OccasionalThingMaker/rudder-pedals/Pictures/3.jpg

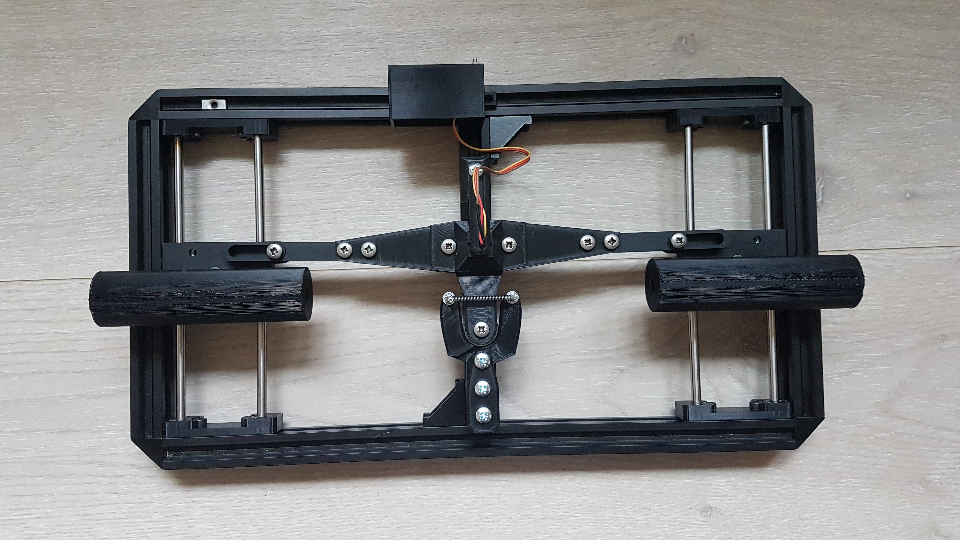
Pictures/3.jpg
