OccasionalThingMaker/rudder-pedals/STLs/Arm Extender to Carriage Bearing.stl

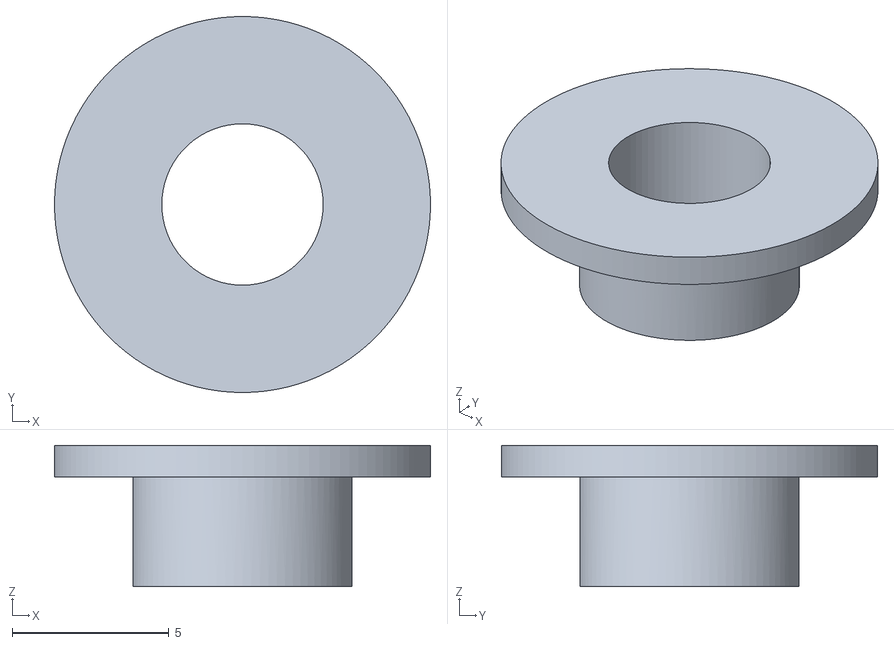
[picture p27: CAD file, 2020-10-21]
STLs/Arm Extender to Carriage Bearing.stl
12.0 x 12.0 x 4.50
