OccasionalThingMaker/rudder-pedals/STLs/Bodnar Box.stl

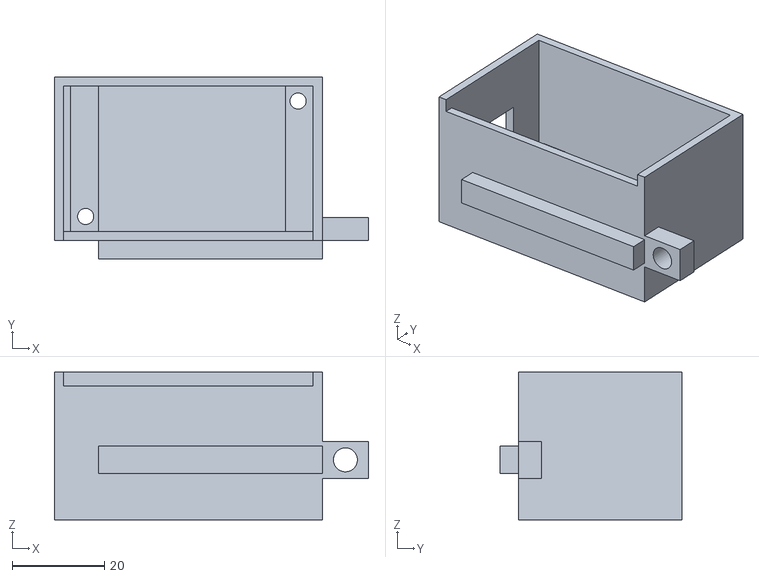
[picture p28: CAD file, 2020-10-21]
STLs/Bodnar Box.stl
68.0 x 39.5 x 32.0
