OccasionalThingMaker/rudder-pedals/STLs/seesaw.stl

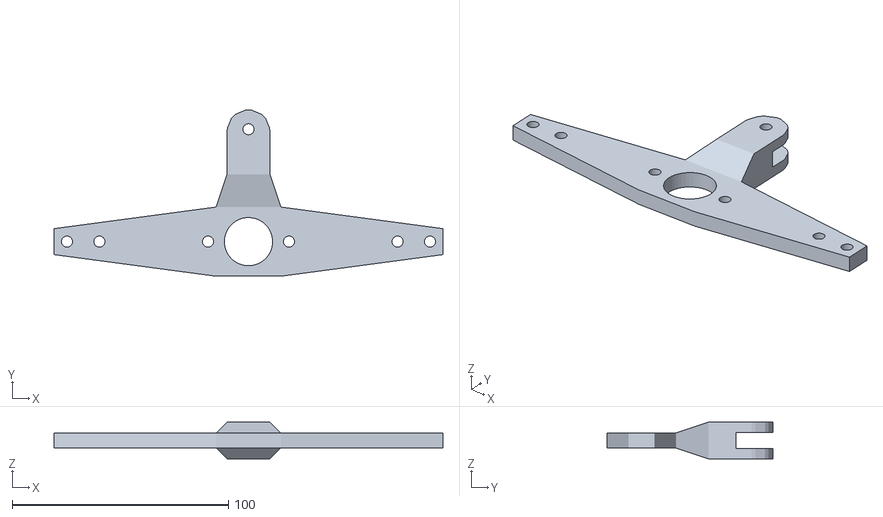
[picture p29: CAD file, 2020-10-21]
STLs/seesaw.stl
180.0 x 77.0 x 17.0
