OccasionalThingMaker/rudder-pedals/STLs/Seesaw Magnet lid.stl

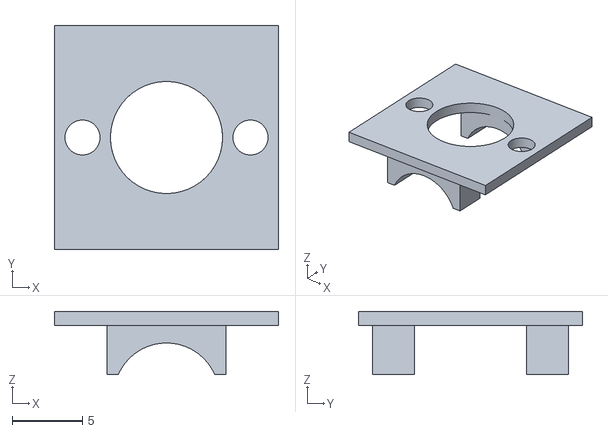
[picture p30: CAD file, 2020-10-21]
STLs/Seesaw Magnet lid.stl
16.0 x 16.0 x 4.50
